sparkfun/SparkFun_LoRaSerial/docs/Original/SparkFun_LoRaSerial_-_AirSpeed_Table-2.png

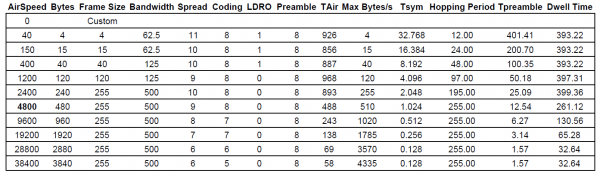
docs/Original/SparkFun_LoRaSerial_-_AirSpeed_Table-2.png
