sparkfun/SparkFun_LoRaSerial/docs/Original/SparkFun_LoRaSerial_-_Reset.png

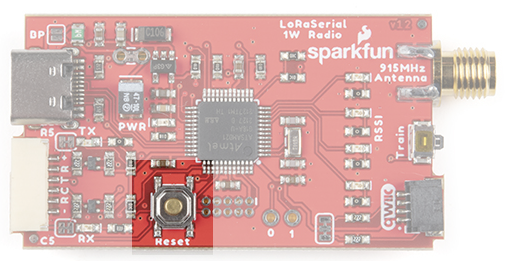
docs/Original/SparkFun_LoRaSerial_-_Reset.png
