sparkfun/SparkFun_LoRaSerial/docs/Original/SparkFun_LoRaSerial_-_RP-SMA_Connector.png

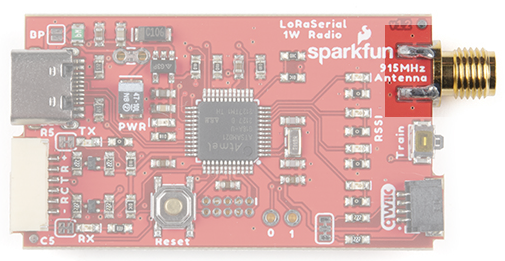
docs/Original/SparkFun_LoRaSerial_-_RP-SMA_Connector.png
