sparkfun/SparkFun_LoRaSerial/docs/Original/SparkFun_LoRaSerial_-_RSSI_LEDs.png

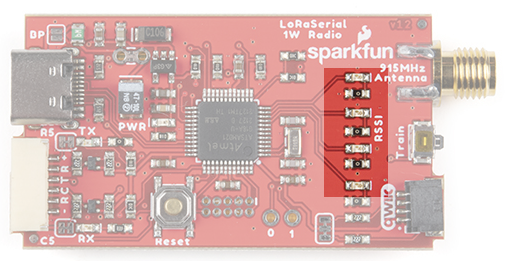
docs/Original/SparkFun_LoRaSerial_-_RSSI_LEDs.png
