sparkfun/SparkFun_LoRaSerial/docs/SparkFun LoRaSerial - AT Command List.png

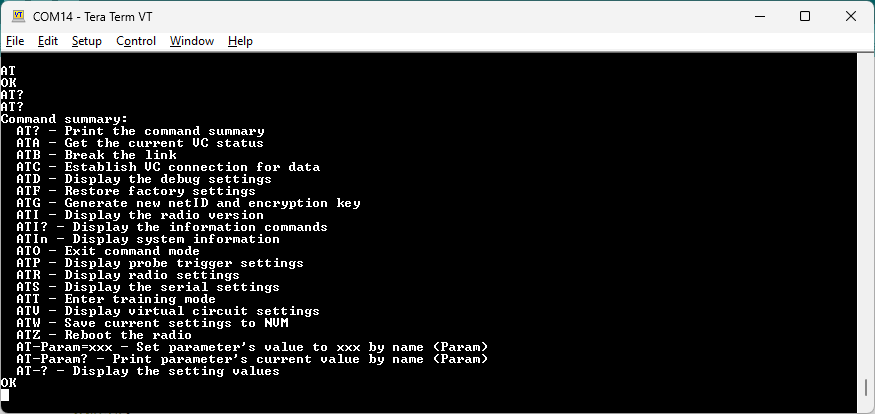
docs/SparkFun LoRaSerial - AT Command List.png
