sparkfun/SparkFun_LoRaSerial/docs/SparkFun LoRaSerial - Device Manager.png

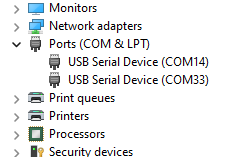
docs/SparkFun LoRaSerial - Device Manager.png
