sparkfun/SparkFun_LoRaSerial/Firmware/LoRaSerial/Commands.ino

//To add a new ATSxx command:
//Add an entry to the "commands" table below

//To add a new commnd prefix such as AT or RT
//Add an entry to the "prefix" table below

//----------------------------------------
//  Data structures
//----------------------------------------

enum {
  TYPE_BOOL = 0,
  TYPE_FLOAT,
  TYPE_KEY,
  TYPE_SPEED_AIR,
  TYPE_SPEED_SERIAL,
  TYPE_U8,
  TYPE_U16,
  TYPE_U32,
};

typedef bool (* COMMAND_ROUTINE)(const char * commandString);
typedef struct
{
  const char * prefix;
  bool supportedInVcMode;
  COMMAND_ROUTINE processCommand;
} COMMAND_PREFIX;

//----------------------------------------
//  Command prefix routines
//----------------------------------------

//Process the AT commands
bool commandAT(const char * commandString)
{
  uint32_t delayMillis;
  long deltaMillis;
  uint8_t id[UNIQUE_ID_BYTES];
  const char * string;
  unsigned long timer;
  VIRTUAL_CIRCUIT * vc = &virtualCircuitList[cmdVc];
  uint8_t vcIndex;

  //'AT'
  if (commandLength == 2)
    return true;

  //AT?, ATA, ATB, ATC, ATG, ATI, ATO, ATZ commands
  if (commandLength == 3)
  {
    switch (commandString[2])
    {
      default:
        return false;

      case ('?'): //Display the command help
        systemPrintln("Command summary:");
        systemPrintln("  AT? - Print the command summary");
        systemPrintln("  ATA - Get the current VC status");
        systemPrintln("  ATB - Break the link");
        systemPrintln("  ATC - Establish VC connection for data");
        systemPrintln("  ATD - Display the debug settings");
        systemPrintln("  ATF - Restore factory settings");
        systemPrintln("  ATG - Generate new netID and encryption key");
        systemPrintln("  ATI - Display the radio version");
        systemPrintln("  ATI? - Display the information commands");
        systemPrintln("  ATIn - Display system information");
        systemPrintln("  ATO - Exit command mode");
        systemPrintln("  ATP - Display probe trigger settings");
        systemPrintln("  ATR - Display radio settings");
        systemPrintln("  ATS - Display the serial settings");
        systemPrintln("  ATT - Enter training mode");
        systemPrintln("  ATV - Display virtual circuit settings");
        systemPrintln("  ATW - Save current settings to NVM");
        systemPrintln("  ATZ - Reboot the radio");
        systemPrintln("  AT-Param=xxx - Set parameter's value to xxx by name (Param)");
        systemPrintln("  AT-Param? - Print parameter's current value by name (Param)");
        systemPrintln("  AT-? - Display the setting values");
        return true;

      case ('A'): //ATA - Get the current VC status
        for (int index = 0; index < MAX_VC; index++)
          vcSendPcStateMessage(index, virtualCircuitList[index].vcState);
        return true;

      case ('B'): //ATB - Break the link

        //Compute the time delay
        delayMillis = (LINK_BREAK_MULTIPLIER + 2) * settings.heartbeatTimeout;

        //Warn the user of the delay
        systemPrint("Delaying ");
        systemPrint(delayMillis / 1000);
        systemPrintln(" seconds to break the link");
        outputSerialData(true);

        //Flag the links as broken
        if (settings.operatingMode == MODE_VIRTUAL_CIRCUIT)
        {
          for (int i = 0; i < MAX_VC; i++)
            if ((virtualCircuitList[i].vcState != VC_STATE_LINK_DOWN) && (i != myVc))
              vcBreakLink(i);
        }
        else if (settings.operatingMode == MODE_POINT_TO_POINT)
        {
          breakLink();
          outputSerialData(true);
        }

        //Idle the system to break the link
        //This is required on the server system which does not request an VC number assignment
        timer = millis();
        while ((millis() - timer) < ((LINK_BREAK_MULTIPLIER + 2) * settings.heartbeatTimeout))
          petWDT();
        changeState(RADIO_RESET);

        //Display the end of the delay
        systemPrintln("Delay done");
        return true;

      case ('C'): //ATC - Establish VC connection for data
        if ((settings.operatingMode != MODE_VIRTUAL_CIRCUIT)
            || (vc->vcState != VC_STATE_LINK_ALIVE))
          return false;
        if (cmdVc == myVc)
          vcChangeState(cmdVc, VC_STATE_CONNECTED);
        else
          vcChangeState(cmdVc, VC_STATE_SEND_UNKNOWN_ACKS);
        return true;

      case ('F'): //ATF - Restore default parameters
        settings = defaultSettings; //Overwrite all system settings with defaults

        validateSettings(); //Modify defaults for each radio type (915, 868, 433, etc)

        tempSettings = settings; //Overwrite all temp settings with defaults
        forceRadioReset = true;

        recordSystemSettings();

        //Clear the unique ID table
        for (vcIndex = 0; vcIndex < MAX_VC; vcIndex++)
          nvmEraseUniqueId(vcIndex);
        return true;

      case ('G'): //ATG - Generate a new netID and encryption key
        generateRandomKeysID(&tempSettings);
        return true;

      case ('I'): //ATI
        //Shows the radio version
        systemPrint("SparkFun LoRaSerial ");
        systemPrint(platformPrefix);
        systemPrint(" v");
        systemPrint(FIRMWARE_VERSION_MAJOR);
        systemPrint(".");
        systemPrintln(FIRMWARE_VERSION_MINOR);
        return true;

      case ('O'): //ATO - Exit command mode
        if (printerEndpoint == PRINT_TO_RF)
          //If we are pointed at the RF link, send ok and wait for response ACK before applying settings
          return true;

        inCommandMode = false; //Return to printing normal RF serial data

        settings = tempSettings; //Apply user's modifications

        if (writeOnCommandExit)
        {
          writeOnCommandExit = false;
          recordSystemSettings();
        }

        //If a setting was applied that requires radio reset, do so
        if (forceRadioReset)
        {
          forceRadioReset = false;
          changeState(RADIO_RESET);
        }

        return true;

      case ('T'): //ATT - Enter training mode
        trainingSettings = tempSettings; //Apply user's modifications
        selectTraining();
        return true;

      case ('W'): //ATW - Write parameters to the flash memory
        writeOnCommandExit = true;
        return true;

      case ('Z'): //ATZ - Reboots the system
        if (writeOnCommandExit)
        {
          settings = tempSettings; //Apply user's modifications
          recordSystemSettings();
        }

        reportOK();
        commandReset();
        return true;
    }
  }

  //ATIx commands
  if (commandString[2] == 'I' && commandLength == 4)
  {
    switch (commandString[3])
    {
      default:
        return false;

      case ('?'): //ATI? - Display the information commands
        systemPrintln("  ATI0 - Show user settable parameters");
        systemPrintln("  ATI1 - Show board variant");
        systemPrintln("  ATI2 - Show firmware version");
        systemPrintln("  ATI3 - Display RSSI value");
        systemPrintln("  ATI4 - Get random byte from RSSI");
        systemPrintln("  ATI5 - Show max possible bytes per second");
        systemPrintln("  ATI6 - Display AES key");
        systemPrintln("  ATI7 - Show current FHSS channel");
        systemPrintln("  ATI8 - Display system unique ID");
        systemPrintln("  ATI9 - Display the maximum datagram size");
        systemPrintln("  ATI10 - Display radio metrics");

        //Virtual circuit information commands
        systemPrintln("  ATI30 - Return myVc value");
        systemPrintln("  ATI31 - Display the VC details");
        systemPrintln("  ATI32 - Dump the NVM unique ID table");
        return true;

      case ('0'): //ATI0 - Show user settable parameters
        displayParameters(0, true);
        return true;

      case ('1'): //ATI1 - Show board variant
        systemPrint("SparkFun LoRaSerial ");
        systemPrint(platformPrefix);
        systemPrint("\r\n");
        return true;

      case ('2'): //ATI2 - Show firmware version
        systemPrint(FIRMWARE_VERSION_MAJOR);
        systemPrint(".");
        systemPrintln(FIRMWARE_VERSION_MINOR);
        return true;

      case ('3'): //ATI3 - Display latest RSSI
        systemPrintln(radio.getRSSI());
        return true;

      case ('4'): //ATI4 - Get random byte from RSSI
        systemPrintln(radio.randomByte());
        return true;

      case ('5'): //ATI5 - Show max possible bytes per second
        systemPrintln(calcMaxThroughput());
        return true;

      case ('6'): //ATI6 - Display currentState
        displayState(radioState);
        return true;

      case ('7'): //ATI7 - Show current FHSS channel
        systemPrintln(channelNumber);
        return true;

      case ('8'): //ATI8 - Display the system's unique ID
        systemPrintUniqueID(myUniqueId);
        systemPrintln();
        return true;

      case ('9'): //ATI9 - Display the maximum datagram size
        systemPrint("Maximum datagram size: ");
        systemPrintln(maxDatagramSize);
        return true;
    }
  }
  if ((commandString[2] == 'I') && (commandString[3] == '1') && (commandLength == 5))
  {
    switch (commandString[4])
    {
      default:
        return false;

      case ('0'): //ATI10 - Display radio metrics
        systemPrint("Radio Metrics @ ");
        systemPrintTimestamp(millis() + timestampOffset);
        systemPrintln();
        if (settings.operatingMode == MODE_POINT_TO_POINT)
        {
          systemPrint("    Link Status: ");
          systemPrintln((radioState >= RADIO_P2P_LINK_UP) ? "Up" : "Down");
          systemPrint("        Last RX:  ");
          systemPrintTimestamp(lastRxDatagram + timestampOffset);
          systemPrintln();
          systemPrint("        First RX: ");
          systemPrintTimestamp(lastLinkUpTime + timestampOffset);
          systemPrintln();
          delayMillis = lastRxDatagram - lastLinkUpTime;
          if (((int)delayMillis) >= 0)
          {
            systemPrint("        Up Time:  ");
            systemPrintTimestamp(delayMillis);
            systemPrintln();
          }
          outputSerialData(true);
          petWDT();
        }

        //Transmitter metrics
        systemPrintln("    Sent");
        systemPrint("        Datagrams: ");
        systemPrintln(datagramsSent);
        systemPrint("        Frames: ");
        systemPrintln(framesSent);
        systemPrint("        Lost Frames: ");
        systemPrintln(lostFrames);
        outputSerialData(true);
        petWDT();

        //Receiver metrics
        systemPrintln("    Received");
        systemPrint("        Frames: ");
        systemPrintln(framesReceived);
        systemPrint("        Datagrams: ");
        systemPrintln(datagramsReceived);
        systemPrint("        Bad CRC: ");
        systemPrintln(badCrc);
        systemPrint("        Bad Frames: ");
        systemPrintln(badFrames);
        systemPrint("        Duplicate Frames: ");
        systemPrintln(duplicateFrames);
        systemPrint("        Insufficient Space: ");
        systemPrintln(insufficientSpace);
        systemPrint("        Net ID Mismatch: ");
        systemPrintln(netIdMismatch);
        systemPrint("        Link failures: ");
        systemPrintln(linkFailures);
        outputSerialData(true);
        petWDT();

        //ACK management metrics
        if (settings.operatingMode == MODE_POINT_TO_POINT)
        {
          vc = &virtualCircuitList[0];
          systemPrintln("    ACK Management");
          systemPrint("        Last RX ACK number: ");
          systemPrintln(vc->rxAckNumber);
          systemPrint("        Next RX ACK number: ");
          systemPrintln(vc->rmtTxAckNumber);
          systemPrint("        Last TX ACK number: ");
          systemPrintln(vc->txAckNumber);
          systemPrint("        ackTimer: ");
          if (ackTimer)
            systemPrintTimestamp(ackTimer + timestampOffset);
          else
            systemPrint("Not Running");
          systemPrintln();
        }
        else if (settings.operatingMode == MODE_VIRTUAL_CIRCUIT)
        {
          systemPrintln("    ACK Management");
          systemPrint("        ackTimer: ");
          if (ackTimer)
          {
            systemPrint("VC ");
            systemPrint(txDestVc);
            systemPrint(", ");
            systemPrintTimestamp(ackTimer + timestampOffset);
            systemPrintln();
          }
          else
            systemPrintln("Not Running");
          systemPrint("    vcConnecting: ");
          systemPrint((int)vcConnecting, HEX);
          if (vcConnecting)
          {
            systemPrintln();
            for (int index = 0; index < MAX_VC; index++)
            {
              if (vcConnecting & (1 << index))
              {
                systemPrint("        VC ");
                if (index < 10)
                  systemWrite(' ');
                systemPrint(index);
                systemPrint(" State: ");
                systemPrintln(vcStateNames[virtualCircuitList[index].vcState]);
              }
            }
          }
          else
            systemPrintln("None");
        }
        outputSerialData(true);
        petWDT();

        //Clock synchronization
        systemPrintln("    Clock Synchronization");
        systemPrint("        ACK Time: ");
        systemPrint(txDataAckUsec);
        systemPrintln(" uSec");
        systemPrint("        FIND_PARTNER Time: ");
        systemPrint(txFindPartnerUsec);
        systemPrintln(" uSec");
        systemPrint("        HEARTBEAT Time: ");
        systemPrint(txHeartbeatUsec);
        systemPrintln(" uSec");
        systemPrint("        SYNC_CLOCKS Time: ");
        systemPrint(txSyncClocksUsec);
        systemPrintln(" uSec");
        systemPrint("        Uptime: ");
        deltaMillis = millis();
        systemPrintTimestamp(deltaMillis);
        systemPrintln();
        systemPrint("        TimeStampOffset: ");
        if (timestampOffset < 0)
        {
          systemPrint("-");
          systemPrintTimestamp(-timestampOffset);
        }
        else
          systemPrintTimestamp(timestampOffset);
        systemPrintln();
        systemPrint("        Adjusted Time: ");
        systemPrintTimestamp(deltaMillis + timestampOffset);
        systemPrintln();
        outputSerialData(true);
        petWDT();

        //Circular buffer metrics
        systemPrintln("    Circular Buffers");
        systemPrint("        serialReceiveBuffer: rxHead: ");
        systemPrint(rxHead);
        systemPrint(", rxTail: ");
        systemPrint(rxTail);
        systemPrint(", ");
        systemPrint(availableRXBytes());
        systemPrintln(" bytes");
        systemPrint("        serialTransmitBuffer: txHead: ");
        systemPrint(txHead);
        systemPrint(", txTail: ");
        systemPrint(txTail);
        systemPrint(", ");
        systemPrint(availableTXBytes());
        systemPrintln(" bytes");
        systemPrint("        radioTxBuffer: radioTxHead: ");
        systemPrint(radioTxHead);
        systemPrint(", radioTxTail: ");
        systemPrint(radioTxTail);
        systemPrint(", ");
        systemPrint(availableRadioTXBytes());
        systemPrintln(" bytes");
        systemPrint("        inCommandMode: ");
        systemPrintln(inCommandMode ? "True" : "False");
        systemPrint("        commandRXBuffer: commandRXHead: ");
        systemPrint(commandRXHead);
        systemPrint(", commandRXTail: ");
        systemPrint(commandRXTail);
        systemPrint(", ");
        systemPrint(availableRXCommandBytes());
        systemPrintln(" bytes");
        systemPrint("        commandTXBuffer: commandTXHead: ");
        systemPrint(commandTXHead);
        systemPrint(", commandTXTail: ");
        systemPrint(commandTXTail);
        systemPrint(", ");
        systemPrint(availableTXCommandBytes());
        systemPrintln(" bytes");
        outputSerialData(true);
        petWDT();

        //Radio metrics
        systemPrintln("    Radio");
        systemPrint("        Channel: ");
        systemPrintln(channelNumber);
        systemPrint("        Frequency: ");
        systemPrint(radioFrequency, 3);
        systemPrint(" MHz");
        if (radioFrequency != channels[channelNumber])
        {
          systemPrint(" = ");
          systemPrint(channels[channelNumber], 3);
          systemPrint(" MHz + ");
          systemPrint((radioFrequency - channels[channelNumber]) * 1000, 0);
          systemPrint(" KHz");
        }
        systemPrintln();
        systemPrint("        maxDwellTime: ");
        systemPrint(settings.maxDwellTime);
        systemPrintln(" mSec");
        if (channelNumber)
        {
          systemPrint("        Next Ch 0 time: ");
          systemPrintTimestamp(millis() + mSecToChannelZero() + timestampOffset);
          int hopCount = settings.numberOfChannels - channelNumber;
          systemPrint(", in ");
          systemPrint(hopCount);
          systemPrintln(" hops");
        }
        systemPrint("        Last Successful Transmit: ");
        if (txSuccessMillis)
        {
          systemPrintTimestamp(txSuccessMillis + timestampOffset);
          systemPrintln();
        }
        else
          systemPrintln("None");
        systemPrint("        Last Transmit Failure: ");
        if (txFailureMillis)
        {
          systemPrintTimestamp(txFailureMillis + timestampOffset);
          systemPrint(", Status: ");
          systemPrint(txFailureState);
          string = getRadioStatusCode(txFailureState);
          if (string)
          {
            systemPrint(", ");
            systemPrint(string);
          }
          systemPrintln();
        }
        else
          systemPrintln("None");
        systemPrint("        Last Successful Receive: ");
        if (rxSuccessMillis)
        {
          systemPrintTimestamp(rxSuccessMillis + timestampOffset);
          systemPrintln();
        }
        else
          systemPrintln("None");
        systemPrint("        Last Receive Failure: ");
        if (rxFailureMillis)
        {
          systemPrintTimestamp(rxFailureMillis + timestampOffset);
          systemPrint(", Status: ");
          systemPrint(rxFailureState);
          string = getRadioStatusCode(rxFailureState);
          if (string)
          {
            systemPrint(", ");
            systemPrint(string);
          }
          systemPrintln();
        }
        else
          systemPrintln("None");
        systemPrint("        radio.startReceive Failure: ");
        if (startReceiveFailureMillis)
        {
          systemPrintTimestamp(startReceiveFailureMillis + timestampOffset);
          systemPrintln();
          systemPrint("        radio.startReceive Status: ");
          systemPrintln(startReceiveFailureState);
        }
        else
          systemPrintln("None");
        systemPrint("        transactionComplete: ");
        systemPrintln(transactionComplete ? "True" : "False");
        systemPrint("        lastReceiveInProcessTrue @ ");
        systemPrintTimestamp(lastReceiveInProcessTrue + timestampOffset);
        systemPrintln();
        systemPrint("        lastModemStatus: ");
        systemPrint(lastModemStatus, HEX);
        systemPrintln();
        systemPrint("        irqFlags: 0x");
        systemPrint(irqFlags, HEX);
        systemPrintln();
        if (irqFlags & 0x80)
          systemPrintln("            RX Timeout");
        if (irqFlags & 0x40)
          systemPrintln("            RX Done");
        if (irqFlags & 0x20)
          systemPrintln("            Payload CRC Error");
        if (irqFlags & 0x10)
          systemPrintln("            Valid Header");
        if (irqFlags & 8)
          systemPrintln("            TX Done");
        if (irqFlags & 4)
          systemPrintln("            CAD Done");
        if (irqFlags & 2)
          systemPrintln("            FHSS Change Channel");
        if (irqFlags & 1)
          systemPrintln("            CAD Detected");
        systemPrint("        receiveInProcess: ");
        systemPrintln(receiveInProcess() ? "True" : "False");
        outputSerialData(true);
        petWDT();

        //Call history
        systemPrintln("    Call History");
        displayRadioCallHistory();
        outputSerialData(true);
        petWDT();

        //State history
        systemPrintln("    State History");
        displayRadioStateHistory();
        return true;
    }
  }
  if ((commandString[2] == 'I') && (commandString[3] == '3') && (commandLength == 5))
  {
    switch (commandString[4])
    {
      default:
        return false;

      case ('0'): //ATI30 - Return myVc value
        systemPrintln();
        systemPrint("myVc: ");
        systemPrintln(myVc);
        return true;

      case ('1'): //ATI31 - Display the VC details
        systemPrintTimestamp();
        systemPrint("VC ");
        systemPrint(cmdVc);
        systemPrint(": ");
        if (!vc->flags.valid)
          systemPrintln("Down, Not valid");
        else
        {
          systemPrintln(vcStateNames[vc->vcState]);
          systemPrintTimestamp();
          systemPrint("    ID: ");
          systemPrintUniqueID(vc->uniqueId);
          systemPrintln(vc->flags.valid ? " (Valid)" : " (Invalid)");

          //Heartbeat metrics
          systemPrintTimestamp();
          systemPrintln("    Heartbeats");
          if (cmdVc == myVc)
          {
            systemPrintTimestamp();
            systemPrint("        Next TX: ");
            systemPrintTimestamp(heartbeatTimer + heartbeatRandomTime + timestampOffset);
            systemPrintln();
          }
          systemPrintTimestamp();
          systemPrint("        Last:    ");
          systemPrintTimestamp(vc->lastTrafficMillis + timestampOffset);
          systemPrintln();
          systemPrintTimestamp();
          systemPrint("        First:   ");
          systemPrintTimestamp(vc->firstHeartbeatMillis + timestampOffset);
          systemPrintln();
          systemPrintTimestamp();
          systemPrint("        Up Time: ");
          deltaMillis = vc->lastTrafficMillis - vc->firstHeartbeatMillis;
          if (deltaMillis < 0)
            deltaMillis = -deltaMillis;
          systemPrintTimestamp(deltaMillis);
          systemPrintln();
          outputSerialData(true);
          petWDT();

          //Transmitter metrics
          systemPrintTimestamp();
          systemPrintln("    Sent");
          systemPrintTimestamp();
          systemPrint("        Frames: ");
          systemPrintln(vc->framesSent);
          systemPrintTimestamp();
          systemPrint("        Messages: ");
          systemPrintln(vc->messagesSent);
          outputSerialData(true);
          petWDT();

          //Receiver metrics
          systemPrintTimestamp();
          systemPrintln("    Received");
          systemPrintTimestamp();
          systemPrint("        Frames: ");
          systemPrintln(vc->framesReceived);
          systemPrintTimestamp();
          systemPrint("        Messages: ");
          systemPrintln(vc->messagesReceived);
          systemPrintTimestamp();
          systemPrint("        Bad Lengths: ");
          systemPrintln(vc->badLength);
          systemPrintTimestamp();
          systemPrint("        Link Failures: ");
          systemPrintln(linkFailures);
          outputSerialData(true);
          petWDT();

          //ACK Management metrics
          systemPrintTimestamp();
          systemPrintln("    ACK Management");
          systemPrintTimestamp();
          systemPrint("        Last RX ACK number: ");
          systemPrintln(vc->rxAckNumber);
          systemPrintTimestamp();
          systemPrint("        Next RX ACK number: ");
          systemPrintln(vc->rmtTxAckNumber);
          systemPrintTimestamp();
          systemPrint("        Last TX ACK number: ");
          systemPrintln(vc->txAckNumber);
          if (txDestVc == cmdVc)
          {
            systemPrintTimestamp();
            systemPrint("        ackTimer: ");
            if (ackTimer)
              systemPrintTimestamp(ackTimer + timestampOffset);
            else
              systemPrint("Not Running");
            systemPrintln();
          }
        }
        return true;

      case ('2'): //ATI32 - Dump the NVM unique ID table
        systemPrintln("NVM Unique ID Table");
        for (vcIndex = 0; vcIndex < MAX_VC; vcIndex++)
        {
          systemPrint("    ");
          if (vcIndex < 10)
            systemWrite(' ');
          systemPrint(vcIndex);
          systemPrint(": ");
          if (nvmIsVcUniqueIdSet(vcIndex))
          {
            nvmGetUniqueId(vcIndex, id);
            systemPrintUniqueID(id);
            systemPrintln();
          }
          else
            systemPrintln("Empty");
        }
        return true;
    }
  }
  if ((commandString[2] == 'I') && (commandString[3] == '5') && (commandLength == 5))
  {
    switch (commandString[4])
    {
      default:
        return false;

      case ('0'): //ATI50 - Output 80000 bytes, stop when serial is full
        for (uint16_t line = 0; line < 1000; line++)
        {
          const char * text = "ABCDEFGHIJKLMNOPQRSTUVWXYZABCDEFGHIJKLMNOPQRSTUVWXYZABCDEFGHIJKLMNOPQRSTUV";

          if (line < 100)
            systemWrite('0');
          if (line < 10)
            systemWrite('0');
          systemPrint(line);
          systemWrite(':');
          systemPrintln(text);
        }
        return true;

      case ('1'): //ATI51 - Display the SX1276 registers
        printSX1276Registers();
        return true;
    }
  }

  //Invalid command
  return false;
}

//Send the AT command over RF link
bool sendRemoteCommand(const char * commandString)
{
  //We cannot send a command if not linked
  if (isLinked() == false)
    return false;

  //Move this command into the transmit buffer
  for (int x = 0 ; x < commandLength ; x++)
  {
    commandTXBuffer[commandTXHead++] = commandString[x];
    commandTXHead %= sizeof(commandTXBuffer);
  }
  if (settings.debugSerial)
  {
    systemPrint("sendRemoteCommand moved ");
    systemPrint(commandLength);
    systemPrintln(" from commandBuffer into commandTXBuffer");
  }
  remoteCommandResponse = false;
  waitRemoteCommandResponse = true;
  return true;
}

//----------------------------------------
//  Command prefix table
//----------------------------------------

const COMMAND_PREFIX prefixTable[] = {
  {"ATD",  1, commandDisplayDebug},
  {"ATP",  1, commandDisplayProbe},
  {"ATR",  1, commandDisplayRadio},
  {"ATS",  1, commandDisplaySerial},
  {"ATV",  1, commandDisplayVirtualCircuit},
  {"AT-?", 1, commandDisplayAll},
  {"AT-",  1, commandSetByName},
  {"AT",   1, commandAT},
  {"RT",   0, sendRemoteCommand},
};

const int prefixCount = sizeof(prefixTable) / sizeof(prefixTable[0]);

//----------------------------------------
//  Command processing routine
//----------------------------------------

//Check to see if a valid command has been received
void checkCommand()
{
  char * commandString;
  int index;
  int prefixLength;
  PrinterEndpoints responseDestination;
  uint16_t responseLength;
  bool success;

  //Save previous index
  if (settings.debugSerial)
  {
    responseDestination = printerEndpoint;
    if (responseDestination == PRINT_TO_SERIAL)
      responseLength = txHead;
    else
      responseLength = commandTXHead;
  }

  //Zero terminate the string
  success = false;
  commandBuffer[commandLength] = 0;

  //Remove any whitespace
  commandString = trimCommand();

  //Upper case the command
  for (index = 0; index < commandLength; index++)
    commandString[index] = toupper(commandString[index]);

  //Echo the command
  systemPrintln(commandString);

  //Verify the command length
  if (commandLength >= 2)
  {
    //Locate the correct processing routine for the command prefix
    for (index = 0; index < prefixCount; index++)
    {
      //Skip command types not supported in current mode
      if ((!prefixTable[index].supportedInVcMode) && (settings.operatingMode != MODE_POINT_TO_POINT))
        continue;

      //Locate the prefix
      prefixLength = strlen(prefixTable[index].prefix);
      if (strncmp(commandString, prefixTable[index].prefix, prefixLength) != 0)
        continue;

      //Process the command
      success = prefixTable[index].processCommand(commandString);
      break;
    }
  }
  else if (!commandLength)
    success = true;

  //Print the command failure
  petWDT();
  if (success)
    reportOK();
  else
  {
    systemPrintln("ERROR");
    commandComplete(false);
  }

  //Display the response
  printerEndpoint = PRINT_TO_SERIAL;
  if (settings.debugSerial)
  {
    uint16_t tail;
    tail = responseLength;
    if (responseDestination == PRINT_TO_SERIAL)
    {
      responseLength = (txHead + sizeof(serialTransmitBuffer) - responseLength) % sizeof(serialTransmitBuffer);
      systemPrint("checkCommand placed ");
      systemPrint(responseLength);
      systemPrintln(" command response bytes into serialTransmitBuffer");
    }
    else
    {
      responseLength = (commandTXHead + sizeof(commandTXBuffer) - responseLength) % sizeof(commandTXBuffer);
      systemPrint("checkCommand placed ");
      systemPrint(responseLength);
      systemPrintln(" command response bytes into commandTXBuffer");
    }
  }
  outputSerialData(true);
  petWDT();

  commandLength = 0; //Get ready for next command
}

//Indicate successful command completion
void reportOK()
{
  systemPrintln("OK");
  commandComplete(true);
}

//Notify the host that the command is complete
void commandComplete(bool success)
{
  if (settings.operatingMode == MODE_VIRTUAL_CIRCUIT)
  {
    //Output the serial message header
    systemWrite(START_OF_VC_SERIAL);
    systemWrite(sizeof(VC_RADIO_MESSAGE_HEADER) + sizeof(VC_COMMAND_COMPLETE_MESSAGE));
    systemWrite(PC_COMMAND_COMPLETE);
    systemWrite(myVc);

    //Output the command complete message
    systemWrite(success ? VC_CMD_SUCCESS : VC_CMD_ERROR);
  }
}

//Notify the host of the reset then reboot the system
void commandReset()
{
  if (serialOperatingMode == MODE_VIRTUAL_CIRCUIT)
  {
    //Notify the PC of the serial port failure
    serialOutputByte(START_OF_VC_SERIAL);
    serialOutputByte(3);
    serialOutputByte(PC_SERIAL_RECONNECT);
    serialOutputByte(myVc);
  }
  outputSerialData(true);
  systemFlush();
  systemReset();
}

//Remove any preceeding or following whitespace chars
char * trimCommand()
{
  int index;
  int j;

  //Remove the comment
  for (index = 0; index < commandLength; index++)
  {
    if (commandBuffer[index] == '#')
    {
      commandBuffer[index] = 0;
      commandLength = index;
      break;
    }
  }

  //Remove the white space
  for (index = 0; index < commandLength; index++)
  {
    while (isspace(commandBuffer[index]))
    {
      for (j = index + 1; j < commandLength; j++)
        commandBuffer[j - 1] = commandBuffer[j];
      commandBuffer[--commandLength] = 0;
    }
  }
  return commandBuffer;
}

//Display all of the commands
bool commandDisplayAll(const char * commandString)
{
  displayParameters(0, false);
  return true;
}

//Display only the debugging commands
bool commandDisplayDebug(const char * commandString)
{
  displayParameters('D', false);
  return true;
}

//Display only the trigger probe commands
bool commandDisplayProbe(const char * commandString)
{
  displayParameters('P', false);
  return true;
}

//Display only the radio commands
bool commandDisplayRadio(const char * commandString)
{
  displayParameters('R', false);
  return true;
}

//Display only the serial commands
bool commandDisplaySerial(const char * commandString)
{
  displayParameters('S', false);
  return true;
}

//Display only the virtual circuit commands
bool commandDisplayVirtualCircuit(const char * commandString)
{
  displayParameters('V', false);
  return true;
}

//----------------------------------------
//  Data validation routines
//----------------------------------------

//Validate a bandwidth value
bool valBandwidth (void * value, uint32_t valMin, uint32_t valMax)
{
  double doubleSettingValue = *(double *)value;

  UNUSED(valMin);
  UNUSED(valMax);

  //Some doubles get rounded incorrectly
  return (((doubleSettingValue * 100) == 1040)
          || (doubleSettingValue == 15.6)
          || ((doubleSettingValue * 100) == 2080)
          || (doubleSettingValue == 31.25)
          || (doubleSettingValue == 41.7)
          || (doubleSettingValue == 62.5)
          || (doubleSettingValue == 125.0)
          || (doubleSettingValue == 250.0)
          || (doubleSettingValue == 500.0));
}

//Validate a maximum frequency value
bool valFreqMax (void * value, uint32_t valMin, uint32_t valMax)
{
  double doubleSettingValue = *(double *)value;

  UNUSED(valMin);

  return ((doubleSettingValue >= settings.frequencyMin) && (doubleSettingValue <= (double)valMax));
}

//Validate a minimum frequency value
bool valFreqMin (void * value, uint32_t valMin, uint32_t valMax)
{
  double doubleSettingValue = *(double *)value;

  UNUSED(valMax);

  return ((doubleSettingValue >= (double)valMin) && (doubleSettingValue <= settings.frequencyMax));
}

//Validate an integer value
bool valInt (void * value, uint32_t valMin, uint32_t valMax)
{
  uint32_t settingValue = *(uint32_t *)value;

  return ((settingValue >= valMin) && (settingValue <= valMax));
}

//Validate an encryption key value
bool valKey (void * value, uint32_t valMin, uint32_t valMax)
{
  unsigned int length;
  char * str = (char *)value;
  char * strEnd;

  UNUSED(valMin);
  UNUSED(valMax);

  //Validate the length of the encryption key
  length = strlen(str);
  if (length != (2 * sizeof(settings.encryptionKey)))
    return false;

  //Validate the characters in the encryption key
  strEnd = &str[length];
  if (strlen(str) == length)
  {
    while (str < strEnd)
    {
      if (charToHex(*str) < 0)
        break;
      str++;
    }
    if (str >= strEnd)
      return true;
  }
  return false;
}

//Validate the server value
bool valServer (void * value, uint32_t valMin, uint32_t valMax)
{
  uint32_t settingValue = *(uint32_t *)value;
  bool valid;
  int8_t vcIndex;

  //Validate the value
  valid = valInt(value, valMin, valMax);

  //Check for a change from client to server
  if (valid && (!settings.server) && settingValue)
  {
    //Clear the unique ID table in NVM
    for (vcIndex = 1; vcIndex < MAX_VC; vcIndex++)
      if (nvmIsVcUniqueIdSet(vcIndex))
        nvmEraseUniqueId(vcIndex);

    //Set our address as the server address
    nvmSaveUniqueId(VC_SERVER, myUniqueId);
  }
  return valid;
}

//Validate the AirSpeed value
bool valSpeedAir (void * value, uint32_t valMin, uint32_t valMax)
{
  bool valid;
  uint32_t settingValue = *(uint32_t *)value;

  UNUSED(valMin);
  UNUSED(valMax);

  valid = ((settingValue == 40)
           || (settingValue == 150)
           || (settingValue == 400)
           || (settingValue == 1200)
           || (settingValue == 2400)
           || (settingValue == 4800)
           || (settingValue == 9600)
           || (settingValue == 19200)
           || (settingValue == 28800)
           || (settingValue == 38400));
  if (valid)
  {
    //Adjust the settings to match the requested airSpeed
    convertAirSpeedToSettings(&tempSettings, settingValue);
    airSpeed = 0;
    systemPrintln("Warning: AirSpeed overrides bandwidth, coding rate, spread factor,");
    systemPrintln("heartbeatTimeout, and txToRxUsec");
  }
  return valid;
}

//Validate the SerialSpeed value
bool valSpeedSerial (void * value, uint32_t valMin, uint32_t valMax)
{
  uint32_t settingValue = *(uint32_t *)value;

  UNUSED(valMin);
  UNUSED(valMax);

  return ((settingValue == 2400)
          || (settingValue == 4800)
          || (settingValue == 9600)
          || (settingValue == 14400)
          || (settingValue == 19200)
          || (settingValue == 38400)
          || (settingValue == 57600)
          || (settingValue == 115200));
}

//----------------------------------------
//  Command table
//----------------------------------------

const COMMAND_ENTRY commands[] =
{
  /*Debug parameters
    Ltr, All, reset, min, max, digits,    type,         validation,     name,                   setting addr, */
  {'D',   1,   0,    0,   1,    0, TYPE_BOOL,         valInt,         "CopyDebug",            &tempSettings.copyDebug},
  {'D',   1,   0,    0,   1,    0, TYPE_BOOL,         valInt,         "Debug",                &tempSettings.debug},
  {'D',   1,   0,    0,   1,    0, TYPE_BOOL,         valInt,         "DebugDatagrams",       &tempSettings.debugDatagrams},
  {'D',   1,   0,    0,   1,    0, TYPE_BOOL,         valInt,         "DebugHeartbeat",       &tempSettings.debugHeartbeat},
  {'D',   1,   0,    0,   1,    0, TYPE_BOOL,         valInt,         "DebugNvm",             &tempSettings.debugNvm},
  {'D',   1,   0,    0,   1,    0, TYPE_BOOL,         valInt,         "DebugRadio",           &tempSettings.debugRadio},
  {'D',   1,   0,    0,   1,    0, TYPE_BOOL,         valInt,         "DebugReceive",         &tempSettings.debugReceive},
  {'D',   1,   0,    0,   1,    0, TYPE_BOOL,         valInt,         "DebugSerial",          &tempSettings.debugSerial},
  {'D',   1,   0,    0,   1,    0, TYPE_BOOL,         valInt,         "DebugStates",          &tempSettings.debugStates},
  {'D',   1,   0,    0,   1,    0, TYPE_BOOL,         valInt,         "DebugSync",            &tempSettings.debugSync},
  {'D',   1,   0,    0,   1,    0, TYPE_BOOL,         valInt,         "DebugTraining",        &tempSettings.debugTraining},
  {'D',   1,   0,    0,   1,    0, TYPE_BOOL,         valInt,         "DebugTransmit",        &tempSettings.debugTransmit},
  {'D',   1,   0,    0,   1,    0, TYPE_BOOL,         valInt,         "DisplayRealMillis",    &tempSettings.displayRealMillis},
  {'D',   1,   0,    0,   1,    0, TYPE_BOOL,         valInt,         "PrintAckNumbers",      &tempSettings.printAckNumbers},
  {'D',   1,   0,    0,   1,    0, TYPE_BOOL,         valInt,         "PrintChannel",         &tempSettings.printChannel},
  {'D',   1,   0,    0,   1,    0, TYPE_BOOL,         valInt,         "PrintFrequency",       &tempSettings.printFrequency},
  {'D',   1,   0,    0,   1,    0, TYPE_BOOL,         valInt,         "PrintLinkUpDown",      &tempSettings.printLinkUpDown},
  {'D',   1,   0,    0,   1,    0, TYPE_BOOL,         valInt,         "PrintPacketQuality",   &tempSettings.printPacketQuality},
  {'D',   1,   0,    0,   1,    0, TYPE_BOOL,         valInt,         "PrintPktData",         &tempSettings.printPktData},
  {'D',   1,   0,    0,   1,    0, TYPE_BOOL,         valInt,         "PrintRfData",          &tempSettings.printRfData},
  {'D',   1,   0,    0,   1,    0, TYPE_BOOL,         valInt,         "PrintTimestamp",       &tempSettings.printTimestamp},
  {'D',   1,   0,    0,   1,    0, TYPE_BOOL,         valInt,         "PrintTxErrors",        &tempSettings.printTxErrors},

  /*Radio parameters
    Ltr, All, reset, min, max, digits,    type,         validation,     name,                   setting addr */
  {'R',   0,   1,    0,   0,    0, TYPE_SPEED_AIR,    valSpeedAir,    "AirSpeed",             &airSpeed},
  {'R',   0,   1,    0,   1,    0, TYPE_BOOL,         valInt,         "AutoTune",             &tempSettings.autoTuneFrequency},
  {'R',   0,   1,    0,   0,    2, TYPE_FLOAT,        valBandwidth,   "Bandwidth",            &tempSettings.radioBandwidth},
  {'R',   0,   1,    5,   8,    0, TYPE_U8,           valInt,         "CodingRate",           &tempSettings.radioCodingRate},
  {'R',   0,   1,    0,   1,    0, TYPE_BOOL,         valInt,         "FrequencyHop",         &tempSettings.frequencyHop},
  {'R',   0,   1,    0, 931,    3, TYPE_FLOAT,        valFreqMax,     "FrequencyMax",         &tempSettings.frequencyMax},
  {'R',   0,   1,  900,   0,    3, TYPE_FLOAT,        valFreqMin,     "FrequencyMin",         &tempSettings.frequencyMin},
  {'R',   0,   1,   10, 65535,  0, TYPE_U16,          valInt,         "MaxDwellTime",         &tempSettings.maxDwellTime},
  {'R',   0,   1,    1, 255,    0, TYPE_U8,           valInt,         "NumberOfChannels",     &tempSettings.numberOfChannels},
  {'R',   0,   1,    6, 65535,  0, TYPE_U16,          valInt,         "PreambleLength",       &tempSettings.radioPreambleLength},
  {'R',   0,   1,    6,  12,    0, TYPE_U8,           valInt,         "SpreadFactor",         &tempSettings.radioSpreadFactor},
  {'R',   0,   1,    0, 255,    0, TYPE_U8,           valInt,         "SyncWord",             &tempSettings.radioSyncWord},
  {'R',   0,   1,   14,  30,    0, TYPE_U8,           valInt,         "TxPower",              &tempSettings.radioBroadcastPower_dbm},
  {'R',   0,   1,    0, 999999, 0, TYPE_U32,          valInt,         "TxToRxUsec",           &tempSettings.txToRxUsec},

  /*Radio protocol parameters
    Ltr, All, reset, min, max, digits,    type,         validation,     name,                   setting addr */
  {'R',   0,   1,    0,   1,    0, TYPE_BOOL,         valInt,         "DataScrambling",       &tempSettings.dataScrambling},
  {'R',   0,   1,    0,   1,    0, TYPE_BOOL,         valInt,         "EnableCRC16",          &tempSettings.enableCRC16},
  {'R',   0,   1,    0,   1,    0, TYPE_BOOL,         valInt,         "EncryptData",          &tempSettings.encryptData},
  {'R',   0,   1,    0,   0,    0, TYPE_KEY,          valKey,         "EncryptionKey",        &tempSettings.encryptionKey},
  {'R',   0,   0,    0, 255,    0, TYPE_U8,           valInt,         "FramesToYield",        &tempSettings.framesToYield},
  {'R',   0,   0,  250, 65535,  0, TYPE_U16,          valInt,         "HeartBeatTimeout",     &tempSettings.heartbeatTimeout},
  {'R',   0,   0,    0, 255,    0, TYPE_U8,           valInt,         "MaxResends",           &tempSettings.maxResends},
  {'R',   0,   1,    0, 255,    0, TYPE_U8,           valInt,         "NetID",                &tempSettings.netID},
  {'R',   0,   1,    0,   2,    0, TYPE_U8,           valInt,         "OperatingMode",        &tempSettings.operatingMode},
  {'R',   0,   1,    0, 1000,   0, TYPE_U16,          valInt,         "OverHeadtime",         &tempSettings.overheadTime},
  {'R',   1,   0,    0, 255,    0, TYPE_U8,           valInt,         "SelectLedUse",         &tempSettings.selectLedUse},
  {'R',   0,   0,    0,   1,    0, TYPE_BOOL,         valServer,      "Server",               &tempSettings.server},
  {'R',   0,   1,    0,   1,    0, TYPE_BOOL,         valInt,         "VerifyRxNetID",        &tempSettings.verifyRxNetID},

  /*Serial parameters
    Ltr, All, reset, min, max, digits,    type,         validation,     name,                   setting addr */
  {'S',   0,   0,    0,   1,    0, TYPE_BOOL,         valInt,         "CopySerial",           &tempSettings.copySerial},
  {'S',   0,   0,    0,   1,    0, TYPE_BOOL,         valInt,         "Echo",                 &tempSettings.echo},
  {'S',   0,   0,    0,   1,    0, TYPE_BOOL,         valInt,         "FlowControl",          &tempSettings.flowControl},
  {'S',   0,   0,    0,   1,    0, TYPE_BOOL,         valInt,         "InvertCts",            &tempSettings.invertCts},
  {'S',   0,   0,    0,   1,    0, TYPE_BOOL,         valInt,         "InvertRts",            &tempSettings.invertRts},
  {'S',   0,   0,    0, SERIAL_RX_BUFFER_SIZE, 0, TYPE_U16, valInt,   "RTSOffBytes",            &tempSettings.rtsOffBytes},
  {'S',   0,   0,    0, SERIAL_RX_BUFFER_SIZE, 0, TYPE_U16, valInt,   "RTSOnBytes",            &tempSettings.rtsOnBytes},
  {'S',   0,   0,   10, 2000,   0, TYPE_U16,          valInt,         "SerialDelay",          &tempSettings.serialTimeoutBeforeSendingFrame_ms},
  {'S',   0,   0,    0,   0,    0, TYPE_SPEED_SERIAL, valSpeedSerial, "SerialSpeed",          &tempSettings.serialSpeed},
  {'S',   0,   0,    0,   1,    0, TYPE_BOOL,         valInt,         "UsbSerialWait",        &tempSettings.usbSerialWait},

  /*Training parameters
    Ltr, All, reset, min, max, digits,    type,         validation,     name,                   setting addr */
  {'R',   0,   1,    1, 255,    0, TYPE_U8,           valInt, "ClientFindPartnerRetryInterval", &tempSettings.clientFindPartnerRetryInterval},
  {'R',   0,   0,    0,   0,    0, TYPE_KEY,          valKey,         "TrainingKey",          &tempSettings.trainingKey},
  {'R',   0,   0,    1, 255,    0, TYPE_U8,           valInt,         "TrainingTimeout",      &tempSettings.trainingTimeout},

  /*Trigger parameters
    Ltr, All, reset, min, max, digits,    type,         validation,     name,                   setting addr */
  {'P',   1,   0,    0,   1,    0, TYPE_BOOL,         valInt,         "CopyTriggers",         &tempSettings.copyTriggers},
  {'P',   1,   0,    0, 0xffffffff, 0, TYPE_U32,      valInt,         "TriggerEnable_31-0",   &tempSettings.triggerEnable},
  {'P',   1,   0,    0, 0xffffffff, 0, TYPE_U32,      valInt,         "TriggerEnable_63-32",  &tempSettings.triggerEnable2},
  {'P',   1,   0,    1, 255,    0, TYPE_U8,           valInt,         "TriggerWidth",         &tempSettings.triggerWidth},
  {'P',   1,   0,    0,   1,    0, TYPE_BOOL,         valInt,     "TriggerWidthIsMultiplier", &tempSettings.triggerWidthIsMultiplier},

  /*Virtual circuit parameters
    Ltr, All, reset, min, max, digits,    type,         validation,     name,                   setting addr */
  {'V',   0,   0,    0, MAX_VC - 1, 0, TYPE_U8,         valInt,         "CmdVC",                &cmdVc},
};

const int commandCount = sizeof(commands) / sizeof(commands[0]);

//----------------------------------------
//  ATSxx routines
//----------------------------------------

//Display a command
void commandDisplay(const COMMAND_ENTRY * command)
{
  //Print the setting value
  switch (command->type)
  {
    case TYPE_BOOL:
      systemPrint((uint8_t)(*(bool *)(command->setting)));
      break;
    case TYPE_FLOAT:
      systemPrint(*((float *)(command->setting)), command->digits);
      break;
    case TYPE_KEY:
      displayEncryptionKey((uint8_t *)(command->setting));
      break;
    case TYPE_U8:
      systemPrint(*(uint8_t *)(command->setting));
      break;
    case TYPE_U16:
      systemPrint(*(uint16_t *)(command->setting));
      break;
    case TYPE_SPEED_AIR:
    case TYPE_SPEED_SERIAL:
    case TYPE_U32:
      systemPrint(*(uint32_t *)(command->setting));
      break;
  }
  systemPrintln();
}

//Set or display the parameter by name
bool commandSetByName(const char * commandString)
{
  const char * buffer;
  const COMMAND_ENTRY * command;
  int index;
  int nameLength;
  int number;
  const char * param;
  int paramLength;
  int table;

  //Determine the parameter name length
  param = &commandString[3];
  buffer = param;
  paramLength = 0;
  while (*buffer && (*buffer != '=') && (*buffer != '?'))
  {
    buffer++;
    paramLength += 1;
  }

  command = NULL;
  for (index = 0; index < commandCount; index++)
  {
    nameLength = strlen(commands[index].name);
    if (nameLength == paramLength)
    {
      //Compare the parameter names
      if (strnicmp(param, commands[index].name, nameLength) == 0)
      {
        command = &commands[index];
        break;
      }
    }
  }

  //Verify that the parameter was found
  if (!command)
    //Report the error
    return false;

  //Process this command
  return commandSetOrDisplayValue(command, buffer);
}

//Set or display the command
bool commandSetOrDisplayValue(const COMMAND_ENTRY * command, const char * buffer)
{
  const char * digit;
  double doubleSettingValue;
  uint32_t settingValue;
  bool valid;

  do {
    //Is this a display request
    if ((*buffer == 0) || (strcmp(buffer, "?") == 0))
    {
      commandDisplay(command);
      return true;
    }

    //Make sure the command has the proper syntax
    if (*buffer++ != '=')
      break;

    //Verify the input value
    for (digit = buffer; *digit != 0; digit++)
      if ((*digit < '0') || (*digit > '9'))
      {
        //Floating point values may contain a decimal point
        if ((command->type == TYPE_FLOAT) && (*digit == '.'))
          continue;

        //Hexadecimal values may contain A through F
        if ((toupper(*digit) >= 'A') && (toupper(*digit) <= 'F')
            && (command->type == TYPE_KEY))
          continue;
        break;
      }
    if (*digit)
      break;

    //Get the value
    doubleSettingValue = strtod(buffer, NULL);
    settingValue = doubleSettingValue;

    //Validate and set the value
    valid = false;
    switch (command->type)
    {
      case TYPE_BOOL:
        valid = command->validate((void *)&settingValue, command->minValue, command->maxValue);
        if (valid)
          *(bool *)(command->setting) = (bool)settingValue;
        break;
      case TYPE_FLOAT:
        valid = command->validate((void *)&doubleSettingValue, command->minValue, command->maxValue);
        if (valid)
          *((float *)(command->setting)) = doubleSettingValue;
        break;
      case TYPE_KEY:
        valid = command->validate((void *)buffer, command->minValue, command->maxValue);
        if (valid)
          for (uint32_t x = 0; x < (2 * AES_KEY_BYTES); x += 2)
            ((uint8_t *)command->setting)[x / 2] = charHexToDec(buffer[x], buffer[x + 1]);
        break;
      case TYPE_SPEED_AIR:
      case TYPE_SPEED_SERIAL:
      case TYPE_U32:
        valid = command->validate((void *)&settingValue, command->minValue, command->maxValue);
        if (valid)
          *(uint32_t *)(command->setting) = settingValue;
        break;
      case TYPE_U8:
        valid = command->validate((void *)&settingValue, command->minValue, command->maxValue);
        if (valid)
          *(uint8_t *)(command->setting) = (uint8_t)settingValue;
        break;
      case TYPE_U16:
        valid = command->validate((void *)&settingValue, command->minValue, command->maxValue);
        if (valid)
          *(uint16_t *)(command->setting) = (uint16_t)settingValue;
        break;
    }
    if (valid == false)
      break;

    //See if this command requires a radio reset to be apply
    if (valid && command->forceRadioReset)
      forceRadioReset = true;

    //The parameter was successfully set
    return true;
  } while (0);

  //Report the error
  return false;
}

//Display the encryption key
void displayEncryptionKey(uint8_t * key)
{
  for (uint8_t index = 0 ; index < sizeof(settings.encryptionKey) ; index++)
    systemPrint(key[index], HEX);
}

//Show current settings in user friendly way
void displayParameters(char letter, bool displayAll)
{
  int index;
  uint8_t sortOrder[commandCount];
  uint8_t temp;
  int x;

  //Set the default sort order
  for (index = 0; index < commandCount; index++)
    sortOrder[index] = index;

  //Perform a bubble sort if requested
  for (index = 0; index < commandCount; index++)
    for (x = index + 1; x < commandCount; x++)
      if (stricmp(commands[sortOrder[index]].name, commands[sortOrder[x]].name) > 0)
      {
        temp = sortOrder[index];
        sortOrder[index] = sortOrder[x];
        sortOrder[x] = temp;
      }

  //Print the parameters
  for (index = 0; index < commandCount; index++)
  {
    if (displayAll || (letter == commands[sortOrder[index]].letter)
        || ((letter == 0) && (!commands[sortOrder[index]].requireAll)))
    {
      petWDT(); //Printing may take longer than WDT at 9600, so pet the WDT.

      if (inCommandMode && (printerEndpoint == PRINT_TO_RF))
        systemPrint("R"); //If someone is asking for our settings over RF, respond with 'R' style settings
      else
        systemPrint("A");

      systemPrint("T-");
      systemPrint(commands[sortOrder[index]].name);
      systemPrint("=");
      commandDisplay(&commands[sortOrder[index]]);
    }
  }
}
