sparkfun/SparkFun_LoRaSerial/Firmware/LoRaSerial/System.ino

//Copy the string into the serialTransmitBuffer or command response buffer (commandTXBuffer)
void systemPrint(const char* string)
{
  uint16_t length;

  length = strlen(string);
  for (uint16_t x = 0 ; x < length ; x++)
    serialOutputByte(string[x]);
}

//Print a string with a carriage return and linefeed
void systemPrintln(const char* value)
{
  systemPrint(value);
  systemPrint("\r\n");
}

//Print an integer value
void systemPrint(int value)
{
  char temp[20];
  sprintf(temp, "%d", value);
  systemPrint(temp);
}

//Print an integer value as HEX or decimal
void systemPrint(int value, uint8_t printType)
{
  char temp[20];

  if (printType == HEX)
    sprintf(temp, "%08x", value);
  else if (printType == DEC)
    sprintf(temp, "%d", value);

  systemPrint(temp);
}

//Print a uint32_t value as HEX or decimal
void systemPrint(uint32_t value, uint8_t printType)
{
  char temp[20];

  if (printType == HEX)
    sprintf(temp, "%08x", value);
  else if (printType == DEC)
    sprintf(temp, "%lu", value);

  systemPrint(temp);
}

//Print a uint32_t value as HEX or decimal
void systemPrintln(uint32_t value, uint8_t printType)
{
  systemPrint(value, printType);
  systemPrintln();
}

//Print an integer value with a carriage return and line feed
void systemPrintln(int value)
{
  systemPrint(value);
  systemPrint("\r\n");
}

//Print an 8-bit value as HEX or decimal
void systemPrint(uint8_t value, uint8_t printType)
{
  char temp[20];

  if (printType == HEX)
    sprintf(temp, "%02X", value);
  else if (printType == DEC)
    sprintf(temp, "%d", value);

  systemPrint(temp);
}

//Print an 8-bit value as HEX or decimal with a carriage return and linefeed
void systemPrintln(uint8_t value, uint8_t printType)
{
  systemPrint(value, printType);
  systemPrint("\r\n");
}

//Print a 16-bit value as HEX or decimal
void systemPrint(uint16_t value, uint8_t printType)
{
  char temp[20];

  if (printType == HEX)
    sprintf(temp, "%04X", value);
  else if (printType == DEC)
    sprintf(temp, "%d", value);

  systemPrint(temp);
}

//Print a 16-bit value as HEX or decimal with a carriage return and linefeed
void systemPrintln(uint16_t value, uint8_t printType)
{
  systemPrint(value, printType);
  systemPrint("\r\n");
}

//Print a floating point value with a specified number of decimal places
void systemPrint(float value, uint8_t decimals)
{
  char temp[20];
  sprintf(temp, "%.*f", decimals, value);
  systemPrint(temp);
}

//Print a floating point value with a specified number of decimal places and a
//carriage return and linefeed
void systemPrintln(float value, uint8_t decimals)
{
  systemPrint(value, decimals);
  systemPrint("\r\n");
}

//Print a double precision floating point value with a specified number of decimal
//places
void systemPrint(double value, uint8_t decimals)
{
  char temp[300];
  sprintf(temp, "%.*g", decimals, value);
  systemPrint(temp);
}

//Print a double precision floating point value with a specified number of decimal
//places and a carriage return and linefeed
void systemPrintln(double value, uint8_t decimals)
{
  systemPrint(value, decimals);
  systemPrint("\r\n");
}

//Print a carriage return and linefeed
void systemPrintln()
{
  systemPrint("\r\n");
}

//Print a timestamp value: days hours:minutes:seconds.milliseconds
void systemPrintTimestamp(unsigned int milliseconds)
{
  unsigned int seconds;
  unsigned int minutes;
  unsigned int hours;
  unsigned int days;
  unsigned int total;

  petWDT();

  //Compute the values for display
  seconds = milliseconds / 1000;
  minutes = seconds / 60;
  hours = minutes / 60;
  days = hours / 24;

  total = days * 24;
  hours -= total;

  total = (total + hours) * 60;
  minutes -= total;

  total = (total + minutes) * 60;
  seconds -= total;

  total = (total + seconds) * 1000;
  milliseconds -= total;

  //Print the days
  if (days < 10) systemPrint(" ");
  if (days)
    systemPrint(days);
  else
    systemPrint(" ");
  systemPrint(" ");

  //Print the time
  if (hours < 10) systemPrint(" ");
  systemPrint(hours);
  systemPrint(":");
  if (minutes < 10) systemPrint("0");
  systemPrint(minutes);
  systemPrint(":");
  if (seconds < 10) systemPrint("0");
  systemPrint(seconds);
  systemPrint(".");
  if (milliseconds < 100) systemPrint("0");
  if (milliseconds < 10) systemPrint("0");
  systemPrint(milliseconds);
  petWDT();
}

//Print a timestamp value with an offset
void systemPrintTimestamp()
{
  unsigned int milliseconds;

  if (settings.printTimestamp)
  {
    //Get the clock value
    milliseconds = millis();

    //Offset the value for display
    if (!settings.displayRealMillis)
      milliseconds += timestampOffset;

    //Print the time
    systemPrintTimestamp(milliseconds);
    systemPrint(": ");
  }
}

//Print the unique ID value
void systemPrintUniqueID(uint8_t * uniqueID)
{
  int index;

  //Display in the same byte order as dump output
  for (index = 0; index < UNIQUE_ID_BYTES; index++)
    systemPrint(uniqueID[index], HEX);
}

//Output a byte to the serial port
void systemWrite(uint8_t value)
{
  serialOutputByte(value);
}

//Output a buffer of the specified length to the serial port
void systemWrite(uint8_t * buffer, uint16_t length)
{
  uint8_t * end;

  //Output the entire buffer ignoring contents
  end = &buffer[length];
  while (buffer < end)
    serialOutputByte(*buffer++);
}

//Ensure all serial output has been transmitted, FIFOs are empty
void systemFlush()
{
  arch.serialFlush();
}

//Read a byte from the serial port
uint8_t systemRead()
{
  return (arch.serialRead());
}

//Check the train button and change state accordingly
void updateButton()
{
  bool buttonPressed;
  static bool buttonWasPressed;
  uint32_t deltaTime;
  static Settings originalSettings;

  if (trainBtn != NULL)
  {
    //Determine the previous state of the button
    buttonPressed = trainBtn->read();

    //Determine the current button state
    if (buttonWasPressed)
    {
      deltaTime = millis() - buttonPressedTime;

      //Check for reset to factory settings
      if (deltaTime >= trainButtonFactoryResetTime)
      {
        //Erase the EEPROM
        nvmErase();

        //Reboot the radio
        commandReset();
      }

      if (!buttonPressed)
      {
        //Button just released
        settings = originalSettings;

        //Starting training or exiting training via the button is only possible
        //when the radio is not in command mode!
        if (!inCommandMode)
        {
          //Check for server training request
          if (deltaTime >= trainButtonServerTime)
          {
            //Set the training settings
            trainingSettings = settings;
            inTraining = true;
            if (settings.operatingMode == MODE_POINT_TO_POINT)
            {
              //Select a random netID and encryption key
              generateRandomKeysID(&trainingSettings);
            }
            beginTrainingServer();
          }

          //Check for client training request
          else if (deltaTime >= trainButtonClientTime)
          {
            trainingSettings = settings; //Set the training settings
            inTraining = true;
            beginTrainingClient();
          }

          //Exit training
          else
          {
            //The user has stopped training with the button
            if (inTraining)
            {
              inTraining = false;
              changeState(RADIO_RESET);
            }
          }
        }
      }
    }

    //The button was not previously pressed
    else
    {
      //Determine if the button is pressed
      if (buttonPressed)
      {
        //Button just pressed
        buttonPressedTime = millis();

        //Save the previous led state
        if (!inTraining)
        {
            originalSettings = settings;
            settings.selectLedUse = LEDS_BUTTON_PRESS;
        }
      }
    }

    //Save the current button state
    buttonWasPressed = buttonPressed;
  }
}

//Platform specific reset commands
void systemReset()
{
  arch.systemReset();
}

//Display any debug serial data and then loop forever
void waitForever(const char * errorMessage)
{
  //Wait forever
  while (1)
  {
    petWDT();
    blinkErrorLed(errorMessage);
  }
}

//Encrypt a given array in place
void encryptBuffer(uint8_t *bufferToEncrypt, uint8_t arraySize)
{
  gcm.setKey(settings.encryptionKey, sizeof(settings.encryptionKey));
  gcm.setIV(AESiv, sizeof(AESiv));

  gcm.encrypt(bufferToEncrypt, bufferToEncrypt, arraySize);
}

//Decrypt a given array in place
void decryptBuffer(uint8_t *bufferToDecrypt, uint8_t arraySize)
{
  gcm.setKey(settings.encryptionKey, sizeof(settings.encryptionKey));
  gcm.setIV(AESiv, sizeof(AESiv));

  gcm.decrypt(bufferToDecrypt, bufferToDecrypt, arraySize);
}


//IBM Whitening process from Semtech "Software Whitening and CRC on SX12xx Devices" app note
//Removes DC Bias from data with long strings of 1s or 0s
void radioComputeWhitening(uint8_t *buffer, uint16_t bufferSize)
{
  uint8_t WhiteningKeyMSB = 0x01;
  uint8_t WhiteningKeyLSB = 0xFF;
  uint8_t WhiteningKeyMSBPrevious = 0;

  for (uint16_t j = 0 ; j < bufferSize ; j++)
  {
    if (timeToHop == true) //If the channelTimer has expired, move to next frequency
      hopChannel();
    buffer[j] ^= WhiteningKeyLSB;

    for (uint8_t i = 0 ; i < 8 ; i++)
    {
      WhiteningKeyMSBPrevious = WhiteningKeyMSB;
      WhiteningKeyMSB = (WhiteningKeyLSB & 0x01) ^ ((WhiteningKeyLSB >> 5) & 0x01);
      WhiteningKeyLSB = ((WhiteningKeyLSB >> 1 ) & 0xFF) | ((WhiteningKeyMSBPrevious << 7) & 0x80);
    }
  }
}

//Toggle a pin. Used for logic analyzer debugging.
void triggerEvent(uint8_t triggerNumber)
{
  uint8_t triggerBitNumber;
  uint32_t triggerEnable;
  uint16_t triggerWidth;

  //Determine if the trigger pin is enabled
  if (pin_trigger == PIN_UNDEFINED)
    return;

  //Determine which trigger enable to use
  triggerBitNumber = triggerNumber;
  triggerEnable = settings.triggerEnable;
  if (triggerNumber >= 32)
  {
    triggerBitNumber -= 32;
    triggerEnable = settings.triggerEnable2;
  }

  //Determine if the trigger is enabled
  if (triggerEnable & (1 << triggerBitNumber))
  {
    //Determine the trigger pulse width
    triggerWidth = settings.triggerWidth;
    if (settings.triggerWidthIsMultiplier)
      triggerWidth *= (triggerNumber + 1);

    //Output the trigger pulse
    digitalWrite(pin_trigger, LOW);
    delayMicroseconds(triggerWidth);
    digitalWrite(pin_trigger, HIGH);
  }
}

//Copy the contents of settings struct to outgoing array
//Note: All variables in struct_settings must be fully cast (uint16_t, int32_t, etc, not int)
//so that we will have alignment between radios using different platforms (ie ESP32 vs SAMD)
void moveSettingsToPacket(Settings settings, uint8_t* packetBuffer)
{
  //Get a byte pointer that points to the beginning of the struct
  uint8_t *bytePtr = (uint8_t*)&settings;

  for (uint8_t x = 0 ; x < sizeof(settings) ; x++)
    packetBuffer[x] = bytePtr[x];
}

//Used to move an incoming packet into the remoteSettings temp buffer
void movePacketToSettings(Settings settings, uint8_t* packetBuffer)
{
  // Get a byte pointer that points to the beginning of the struct
  uint8_t *bytePtr = (uint8_t*)&settings;

  for (uint8_t x = 0 ; x < sizeof(settings) ; x++)
    bytePtr[x] = packetBuffer[x];
}

//Convert ASCII character to base 16
int8_t charToHex(char a)
{
  a = toupper(a);

  if ('0' <= a && a <= '9') a -= '0';
  else if ('A' <= a && a <= 'F') a = a - 'A' + 10;
  else a = -1;
  return a;
}

//Given two letters, convert to base 10
uint8_t charHexToDec(char a, char b)
{
  a = charToHex(a);
  b = charToHex(b);
  return ((a << 4) | b);
}

//Dump a buffer with offset from buffer start, 16 bytes per row, displaying hex and ASCII
void dumpBuffer(uint8_t * data, int length)
{
  char byte[2];
  int bytes;
  uint8_t * dataEnd;
  uint8_t * dataStart;
  const int displayWidth = 16;
  int index;

  byte[1] = 0;
  dataStart = data;
  dataEnd = &data[length];
  while (data < dataEnd)
  {
    // Display the offset
    systemPrint("    0x");
    systemPrint((uint8_t)(data - dataStart), HEX);
    systemPrint(": ");

    // Determine the number of bytes to display
    bytes = dataEnd - data;
    if (bytes > displayWidth)
      bytes = displayWidth;

    // Display the data bytes in hex
    for (index = 0; index < bytes; index++)
    {
      systemPrint(" ");
      systemPrint(*data++, HEX);
      if (timeToHop == true) //If the channelTimer has expired, move to next frequency
        hopChannel();
      petWDT();
    }

    // Space over to the ASCII display
    for (; index < displayWidth; index++)
    {
      systemPrint("   ");
      if (timeToHop == true) //If the channelTimer has expired, move to next frequency
        hopChannel();
      petWDT();
    }
    systemPrint("  ");

    // Display the ASCII bytes
    data -= bytes;
    for (index = 0; index < bytes; index++) {
      byte[0] = *data++;
      systemPrint(((byte[0] < ' ') || (byte[0] >= 0x7f)) ? "." : byte);
    }
    systemPrintln();
    if (timeToHop == true) //If the channelTimer has expired, move to next frequency
      hopChannel();
    petWDT();
  }
}

//Dump a buffer assuming that it contains text
void dumpBufferRaw(uint8_t * data, int length)
{
  systemPrint("0x ");
  for (int x = 0 ; x < length ; x++)
  {
    systemPrint(data[x], HEX);
    systemPrint(" ");
  }
  systemPrintln();
}

//Dump a circular buffer with offset from buffer start, 16 bytes per row, displaying hex and ASCII
void dumpCircularBuffer(uint8_t * buffer, uint16_t tail, uint16_t bufferLength, int length)
{
  int bytes;
  uint8_t data;
  uint16_t delta;
  const int displayWidth = 16;
  uint16_t i;
  int index;
  uint16_t offset;

  offset = tail;
  while (length > 0)
  {
    //Display the offset
    systemPrint("    0x");
    systemPrint((uint16_t)(offset % bufferLength), HEX);
    systemPrint(": ");

    //Adjust for the offset
    delta = offset % displayWidth;
    if (delta)
    {
      bytes -= delta;
      for (index = 0; index < delta; index++)
      {
        systemPrint("   ");
        if (timeToHop == true) //If the channelTimer has expired, move to next frequency
          hopChannel();
        petWDT();
      }
    }

    //Determine the number of bytes to display
    bytes = length;
    if (bytes > (displayWidth - delta))
      bytes = displayWidth - delta;

    //Display the data bytes in hex
    for (index = 0; index < bytes; index++)
    {
      systemWrite(' ');
      data = buffer[(offset + index) % bufferLength];
      systemPrint(data, HEX);
      if (timeToHop == true) //If the channelTimer has expired, move to next frequency
        hopChannel();
      petWDT();
    }

    //Space over to the ASCII display
    for (; (delta + index) < displayWidth; index++)
    {
      systemPrint("   ");
      if (timeToHop == true) //If the channelTimer has expired, move to next frequency
        hopChannel();
      petWDT();
    }
    systemPrint("  ");

    //Display the ASCII bytes
    for (index = 0; index < delta; index++)
      systemWrite(' ');
    for (index = 0; index < bytes; index++) {
      data = buffer[(offset + index) % bufferLength];
      systemWrite(((data < ' ') || (data >= 0x7f)) ? '.' : data);
    }
    systemPrintln();
    if (timeToHop == true) //If the channelTimer has expired, move to next frequency
      hopChannel();
    petWDT();
    outputSerialData(true);
    offset += bytes;
    length -= bytes;
  }
}

//Update the state of the 4 green LEDs
void setRSSI(uint8_t ledBits)
{
  if (ledBits & 0b0001)
    digitalWrite(pin_green_1_LED, HIGH);
  else
    digitalWrite(pin_green_1_LED, LOW);

  if (ledBits & 0b0010)
    digitalWrite(pin_green_2_LED, HIGH);
  else
    digitalWrite(pin_green_2_LED, LOW);

  if (ledBits & 0b0100)
    digitalWrite(pin_green_3_LED, HIGH);
  else
    digitalWrite(pin_green_3_LED, LOW);

  if (ledBits & 0b1000)
    digitalWrite(pin_green_4_LED, HIGH);
  else
    digitalWrite(pin_green_4_LED, LOW);
}

//Start the cylon LEDs
void startCylonLEDs()
{
  cylonLedPattern = 0b0001;
  cylonPatternGoingLeft = false;
}

//Update the RSSI LED or LEDs
void blinkRadioRssiLed()
{
  unsigned long currentMillis;
  static uint32_t ledPreviousRssiMillis;
  static unsigned long lastCylonBlink; //Controls LED during training
  static int8_t ledRssiPulseWidth; //Target pulse width for LED display

  currentMillis = millis();
  switch (settings.selectLedUse)
  {
    //Update the pattern on the 4 green LEDs
    case LEDS_CYLON:
      //Determine if it is time to update the cylon pattern
      if ((currentMillis - lastCylonBlink) > 75)
      {
        lastCylonBlink = currentMillis;

        //The following shows the cylon pattern in four LEDs
        //
        //     LED3  LED2  LED1  LED0
        //                         X
        //                   X
        //             X
        //       X
        //             X
        //                   X
        //                         X
        //                   X
        //            ...
        //
        //Cylon the RSSI LEDs
        setRSSI(cylonLedPattern);

        //Determine if a change in direction is necessary
        if ((cylonLedPattern == 0b1000) || (cylonLedPattern == 0b0001))
          cylonPatternGoingLeft = cylonPatternGoingLeft ? false : true;

        if (cylonPatternGoingLeft)
          cylonLedPattern <<= 1;
        else
          cylonLedPattern >>= 1;
      }
      break;

    //Update the single RSSI LED
    case LEDS_MULTIPOINT:
    case LEDS_P2P:
    case LEDS_RADIO_USE:
    case LEDS_VC:
      //Check for the start of a new pulse
      if ((currentMillis - ledPreviousRssiMillis) >= LED_MAX_PULSE_WIDTH)
      {
        ledPreviousRssiMillis = currentMillis;

        //Determine the RSSI LED pulse width
        //The RSSI value ranges from -164 to 30 dB
        ledRssiPulseWidth = (150 + rssi) / 10;
        if (ledRssiPulseWidth > 0)
          digitalWrite(GREEN_LED_3, LED_ON);
      }

      //Check for time to turn off the LED
      else if ((currentMillis - ledPreviousRssiMillis) >= ledRssiPulseWidth)
        digitalWrite(GREEN_LED_3, LED_OFF);
      break;

    //Update the 4 green LEDs based upon the RSSI value
    case LEDS_RSSI:
      if (rssi > -70)
        setRSSI(0b1111);
      else if (rssi > -100)
        setRSSI(0b0111);
      else if (rssi > -120)
        setRSSI(0b0011);
      else if (rssi > -150)
        setRSSI(0b0001);
      else
        setRSSI(0);
      break;
  }
}

//Set the serial TX (blue) LED value
void blinkSerialTxLed(bool illuminate)
{
  switch (settings.selectLedUse)
  {
    case LEDS_RSSI:
      if (pin_blue_LED != PIN_UNDEFINED)
      {
        if (illuminate == true)
          digitalWrite(pin_blue_LED, HIGH);
        else
          digitalWrite(pin_blue_LED, LOW);
      }
      break;
  }
}

//Set the serial RX (yellow) LED value
void blinkSerialRxLed(bool illuminate)
{
  switch (settings.selectLedUse)
  {
    case LEDS_RSSI:
      if (illuminate == true)
        digitalWrite(pin_yellow_LED, HIGH);
      else
        digitalWrite(pin_yellow_LED, LOW);
      break;

    case LEDS_VC:
      if (illuminate == true)
        digitalWrite(GREEN_LED_2, HIGH);
      else
        digitalWrite(GREEN_LED_2, LOW);
      break;
  }
}

//Blink the RX LED
void blinkRadioRxLed(bool on)
{
  switch (settings.selectLedUse)
  {
    case LEDS_CYLON:
      if (on)
        digitalWrite(YELLOW_LED, LED_ON);
      else if ((millis() - linkDownTimer) >= RADIO_USE_BLINK_MILLIS)
        digitalWrite(YELLOW_LED, LED_OFF);
      break;

    case LEDS_MULTIPOINT:
    case LEDS_P2P:
    case LEDS_RADIO_USE:
    case LEDS_VC:
      if (on)
        digitalWrite(GREEN_LED_1, LED_ON);
      else if ((millis() - linkDownTimer) >= RADIO_USE_BLINK_MILLIS)
        digitalWrite(GREEN_LED_1, LED_OFF);
      break;
  }
}

//BLink the TX LED
void blinkRadioTxLed(bool on)
{
  switch (settings.selectLedUse)
  {
    case LEDS_CYLON:
      if (on)
        digitalWrite(BLUE_LED, LED_ON);
      else if ((millis() - datagramTimer) >= RADIO_USE_BLINK_MILLIS)
        digitalWrite(BLUE_LED, LED_OFF);
      break;

    case LEDS_MULTIPOINT:
    case LEDS_P2P:
    case LEDS_RADIO_USE:
    case LEDS_VC:
      if (on)
        digitalWrite(GREEN_LED_4, LED_ON);
      else if ((millis() - datagramTimer) >= RADIO_USE_BLINK_MILLIS)
        digitalWrite(GREEN_LED_4, LED_OFF);
      break;
  }
}

//Radio LED display
// Green1: Radio RX data received
// Green2: Receiving HEARTBEATs (link up)
// Green3: RSSI level
// Green4: Radio TX data sent
// Blue: Bad frame received
// Yellow: Bad CRC received
void radioLeds()
{
  uint32_t currentMillis;
  static uint32_t previousBadFrames;
  static uint32_t badFramesMillis;
  static uint32_t previousBadCrc;
  static uint32_t badCrcMillis;

  //Turn off the RX LED to end the blink
  blinkRadioRxLed(false);

  //Turn off the TX LED to end the blink
  blinkRadioTxLed(false);

  //Update the link LED
  digitalWrite(GREEN_LED_2, isLinked() ? LED_ON : LED_OFF);

  //Update the RSSI LED
  blinkRadioRssiLed();

  //Blink the bad frames LED
  currentMillis = millis();
  if (badFrames != previousBadFrames)
  {
    previousBadFrames = badFrames;
    badFramesMillis = currentMillis;
    digitalWrite(BLUE_LED, LED_ON);
  }
  else if (badFramesMillis && ((currentMillis - badFramesMillis) >= RADIO_USE_BLINK_MILLIS))
  {
    badFramesMillis = 0;
    digitalWrite(BLUE_LED, LED_OFF);
  }

  //Blink the bad CRC or duplicate frames LED
  if (settings.enableCRC16 && (badCrc != previousBadCrc))
  {
    previousBadCrc = badCrc;
    badCrcMillis = currentMillis;
    digitalWrite(YELLOW_LED, LED_ON);
  }
  if ((!settings.enableCRC16) && (duplicateFrames != previousBadCrc))
  {
    previousBadCrc = duplicateFrames;
    badCrcMillis = currentMillis;
    digitalWrite(YELLOW_LED, LED_ON);
  }
  else if (badCrcMillis && ((currentMillis - badCrcMillis) >= RADIO_USE_BLINK_MILLIS))
  {
    badCrcMillis = 0;
    digitalWrite(YELLOW_LED, LED_OFF);
  }
}

//Blink the heartbeat LED
void blinkHeartbeatLed(bool on)
{
  static unsigned long ledHeartbeatMillis;

  switch (settings.selectLedUse)
  {
    case LEDS_MULTIPOINT:
    case LEDS_P2P:
    case LEDS_VC:
      if (on)
      {
        digitalWrite(BLUE_LED, LED_ON);
        ledHeartbeatMillis = millis();
      }
      else if ((millis() - ledHeartbeatMillis) > RADIO_USE_BLINK_MILLIS)
        digitalWrite(BLUE_LED, LED_OFF);
      break;
  }
}

//Blink the channel hop LED
void blinkChannelHopLed(bool on)
{
  switch (settings.selectLedUse)
  {
    case LEDS_MULTIPOINT:
    case LEDS_P2P:
    case LEDS_VC:
      if (on)
        digitalWrite(YELLOW_LED, LED_ON);
      else if ((millis() - radioCallHistory[RADIO_CALL_hopChannel]) >= RADIO_USE_BLINK_MILLIS)
        digitalWrite(YELLOW_LED, LED_OFF);
      break;
  }
}

//Blink the error LED
void blinkErrorLed(const char * errorMessage)
{
  uint32_t currentMillis;
  static uint32_t lastToggleMillis;
  static uint8_t flashCount;

#define ERROR_FLASHS_PER_SECOND       10
#define DELAY_BETWEEN_MESSAGES_SECS   15

  //Ouptut the error message on a regular interval
  if (!flashCount)
  {
    flashCount = DELAY_BETWEEN_MESSAGES_SECS * (ERROR_FLASHS_PER_SECOND << 1);
    if (errorMessage)
    {
      systemPrintln(errorMessage);
      outputSerialData(true);
    }
  }

  //Determine if it is time to toggle the error LED
  currentMillis = millis();
  if ((currentMillis - lastToggleMillis) >= (1000 / (ERROR_FLASHS_PER_SECOND << 1)))
  {
    //Toggle the error LED
    lastToggleMillis = currentMillis;
    digitalWrite(YELLOW_LED, !digitalRead(YELLOW_LED));
    flashCount -= 1;
  }
}

//Display the multi-point LED pattern
void multiPointLeds()
{
  //Turn off the RX LED to end the blink
  blinkRadioRxLed(false);

  //Turn off the TX LED to end the blink
  blinkRadioTxLed(false);

  //Update the sync LED
  digitalWrite(GREEN_LED_2, isMultiPointSync() ? LED_ON : LED_OFF);

  //Update the RSSI LED
  blinkRadioRssiLed();

  //Update the hop LED
  if ((millis() - radioCallHistory[RADIO_CALL_hopChannel]) >= RADIO_USE_BLINK_MILLIS)
    digitalWrite(YELLOW_LED, LED_OFF);

  //Update the HEARTBEAT LED
  blinkHeartbeatLed(false);
}

void p2pLeds()
{
  //Turn off the RX LED to end the blink
  blinkRadioRxLed(false);

  //Turn off the TX LED to end the blink
  blinkRadioTxLed(false);

  //Pulse width modulate the RSSI LED (GREEN_LED_3)
  blinkRadioRssiLed();

  //Leave the LINK LED (GREEN_LED_2) off

  //Update the hop LED
  if ((millis() - radioCallHistory[RADIO_CALL_hopChannel]) >= RADIO_USE_BLINK_MILLIS)
    digitalWrite(YELLOW_LED, LED_OFF);

  //Update the HEARTBEAT LED
  blinkHeartbeatLed(false);
}

//Display the VC LED pattern
void vcLeds()
{
  uint32_t currentMillis;
  static uint32_t blinkSyncMillis;

  //Turn off the RX LED to end the blink
  blinkRadioRxLed(false);

  //Turn off the TX LED to end the blink
  blinkRadioTxLed(false);

  //Pulse width modulate the RSSI LED (GREEN_LED_3)
  currentMillis = millis();
  if (virtualCircuitList[VC_SERVER].vcState)
    blinkRadioRssiLed();

#define VC_SYNC_BLINK_RATE      (1000 / 4)

  //Turn on the RSSI LED
  else if (((currentMillis - blinkSyncMillis) >= (VC_SYNC_BLINK_RATE >> 1))
           && (digitalRead(GREEN_LED_3) == LED_OFF))
    digitalWrite(GREEN_LED_3, LED_ON);

  //Turn off the RSSI LED
  else if ((!virtualCircuitList[VC_SERVER].vcState)
           && (((currentMillis - blinkSyncMillis) >= VC_SYNC_BLINK_RATE))
           && (digitalRead(GREEN_LED_3) == LED_ON))
  {
    digitalWrite(GREEN_LED_3, LED_OFF);
    blinkSyncMillis = currentMillis;
  }

  //Serial RX displayed on the LINK LED (GREEN_LED_2) by blinkSerialRxLed

  //Update the hop LED
  if ((millis() - radioCallHistory[RADIO_CALL_hopChannel]) >= RADIO_USE_BLINK_MILLIS)
    digitalWrite(YELLOW_LED, LED_OFF);

  //Update the HEARTBEAT LED
  blinkHeartbeatLed(false);
}

//Update the cylon LEDs
void updateCylonLEDs()
{
  //Display the cylon pattern on the RSSI LEDs
  blinkRadioRssiLed();

  //Use the blue and yellow LEDS to indicate radio activity during training
  //Turn off the RX LED to end the blink
  blinkRadioRxLed(false);

  //Turn off the TX LED to end the blink
  blinkRadioTxLed(false);
}

//Acknowledge the button press
void buttonLeds()
{
  const uint32_t blinkTime = 1000 / 4;  //Blink 4 times per second
  uint8_t on;
  const uint32_t onTime = blinkTime / 2;
  uint32_t pressedMilliseconds;
  uint8_t seconds;

  //Display the number of seconds the button has been pushed
  pressedMilliseconds = millis() - buttonPressedTime;
  seconds = pressedMilliseconds / 1000;
  setRSSI((pressedMilliseconds >= trainButtonFactoryResetTime) ? 15 : seconds);

  if (!inCommandMode)
  {
    //Determine the blink state
    on = (pressedMilliseconds % blinkTime) >= onTime;

    //Determine which LED to blink
    if (pressedMilliseconds >= trainButtonServerTime)
    {
      //Blink the blue LED
      digitalWrite(BLUE_LED, on);
      digitalWrite(YELLOW_LED, 0);
    }
    else if (pressedMilliseconds >= trainButtonClientTime)
      //Blink the yellow LED
      digitalWrite(YELLOW_LED, on);
  }
}

//Update the LED values depending upon the selected display
//This is the only function that touches the LEDs
void updateLeds()
{
  static uint8_t previousLedUse;

  //When changing patterns, start with the LEDs off
  if (previousLedUse != settings.selectLedUse)
  {
    previousLedUse = settings.selectLedUse;
    digitalWrite(GREEN_LED_1, LED_OFF);
    digitalWrite(GREEN_LED_2, LED_OFF);
    digitalWrite(GREEN_LED_3, LED_OFF);
    digitalWrite(GREEN_LED_4, LED_OFF);
    digitalWrite(BLUE_LED, LED_OFF);
    digitalWrite(YELLOW_LED, LED_OFF);
  }

  //Display the LEDs
  switch (settings.selectLedUse)
  {
    //Set LEDs according to RSSI level
    default:
    //Display the RSSI LED pattern
    case LEDS_RSSI:
      blinkRadioRssiLed();
      break;

    //Display the multipoint LED pattern
    case LEDS_MULTIPOINT:
      multiPointLeds();
      break;

    //Display the point-to-point LED pattern
    case LEDS_P2P:
      p2pLeds();
      break;

    //Display the multipoint LED pattern
    case LEDS_VC:
      vcLeds();
      break;

    //Display the cylon LED pattern
    case LEDS_CYLON:
      updateCylonLEDs();
      break;

    //Display the radio use LED pattern
    case LEDS_RADIO_USE:
      radioLeds();
      break;

    case LEDS_BUTTON_PRESS:
      buttonLeds();
      break;

    //Turn off all the LEDs
    case LEDS_ALL_OFF:
      break;

    //Turn on the blue LED for testing
    case LEDS_BLUE_ON:
      digitalWrite(BLUE_LED, LED_ON);
      break;

    //Turn on the yellow LED for testing
    case LEDS_YELLOW_ON:
      digitalWrite(YELLOW_LED, LED_ON);
      break;

    //Turn on the green 1 LED for testing
    case LEDS_GREEN_1_ON:
      digitalWrite(GREEN_LED_1, LED_ON);
      break;

    //Turn on the green 2 LED for testing
    case LEDS_GREEN_2_ON:
      digitalWrite(GREEN_LED_2, LED_ON);
      break;

    //Turn on the green 3 LED for testing
    case LEDS_GREEN_3_ON:
      digitalWrite(GREEN_LED_3, LED_ON);
      break;

    //Turn on the green 4 LED for testing
    case LEDS_GREEN_4_ON:
      digitalWrite(GREEN_LED_4, LED_ON);
      break;

    //Turn on all the LEDs for testing
    case LEDS_ALL_ON:
      digitalWrite(GREEN_LED_1, LED_ON);
      digitalWrite(GREEN_LED_2, LED_ON);
      digitalWrite(GREEN_LED_3, LED_ON);
      digitalWrite(GREEN_LED_4, LED_ON);
      digitalWrite(BLUE_LED, LED_ON);
      digitalWrite(YELLOW_LED, LED_ON);
      break;
  }
}

//Case independent string comparison
int stricmp(const char * str1, const char * str2)
{
  char char1;
  char char2;

  //Do a case insensitive comparison between the two strings
  do {
    char1 = toupper(*str1++);
    char2 = toupper(*str2++);
  } while (char1 && (char1 == char2));

  //Return the difference between the two strings
  return char1 - char2;
}

//Case independent string comparison with specified maximum length
int strnicmp(const char * str1, const char * str2, int length)
{
  char char1;
  char char2;

  //Do a case insensitive comparison between the two strings
  do {
    char1 = toupper(*str1++);
    char2 = toupper(*str2++);
  } while (char1 && (char1 == char2) && --length);

  //Return the difference between the two strings
  return char1 - char2;
}

//Display the RSSI, SNR and frequency error values
void printPacketQuality()
{
  if (settings.printPacketQuality == true)
  {
    systemPrintln();
    systemPrint("R:");
    systemPrint(rssi);
    systemPrint("\tS:");
    systemPrint(radio.getSNR());
    systemPrint("\tfE:");
    systemPrint(radio.getFrequencyError());
    systemPrintln();
  }
}

//Toggle a pin. Used for logic analyzer debugging.
void triggerFrequency(uint16_t frequency)
{
  digitalWrite(pin_trigger, LOW);
  delayMicroseconds(frequency);
  digitalWrite(pin_trigger, HIGH);
}

//Verify the VC_STATE_TYPE enums against the vcStateNames table
const char * verifyVcStateNames()
{
  bool valid;

  //Verify the length of the vcStateNames table
  valid = (VC_STATE_MAX == (sizeof(vcStateNames) / sizeof(vcStateNames[0])));
  if (!valid)
    return "ERROR: Fix difference between VC_STATE_TYPE and vcStateNames";
  return NULL;
}

//Verify the enums .vs. name tables, stop on failure to force software fix
void verifyTables()
{
  const char * errorMessage;

  do
  {
    //Verify that the state table contains all of the states in increasing order
    errorMessage = verifyRadioStateTable();
    if (errorMessage)
      break;

    //Verify that the datagram type table contains all of the datagram types
    errorMessage = verifyRadioDatagramType();
    if (errorMessage)
      break;

    //Verify the VC state name table
    errorMessage = verifyVcStateNames();
    if (errorMessage)
      break;

    //Verify the RADIO_CALLS enum against the radioCallName
    errorMessage = verifyRadioCallNames();
  } while (0);

  //Handle the error
  if (errorMessage)
    waitForever(errorMessage);
}
